joshajohnson/Hub20/production/1.0/photo.JPG

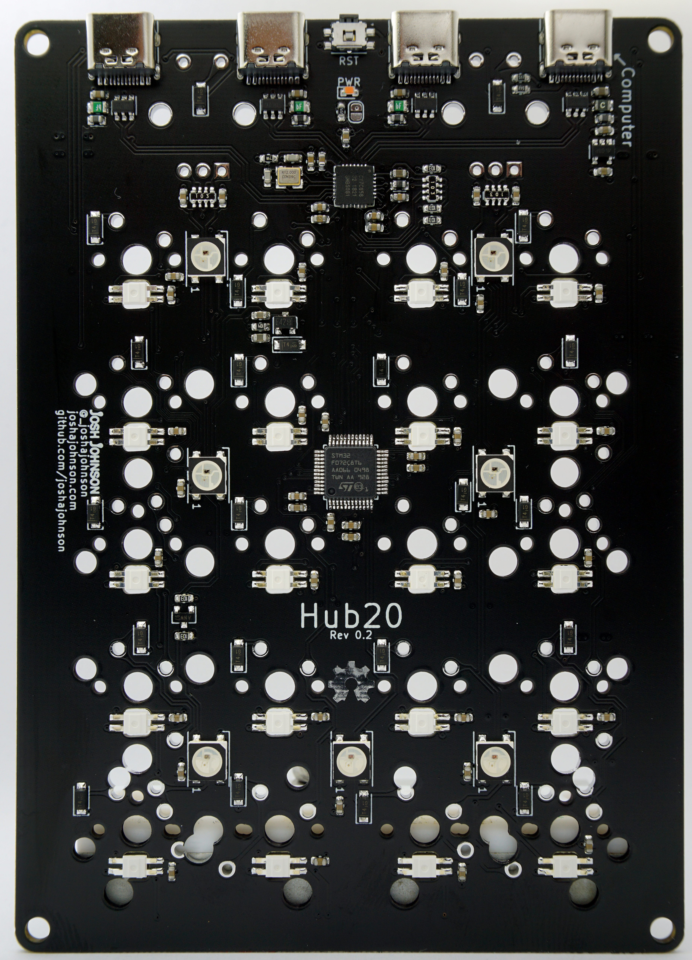
production/1.0/photo.JPG
