joshajohnson/Hub20/production/1.0/render.jpg

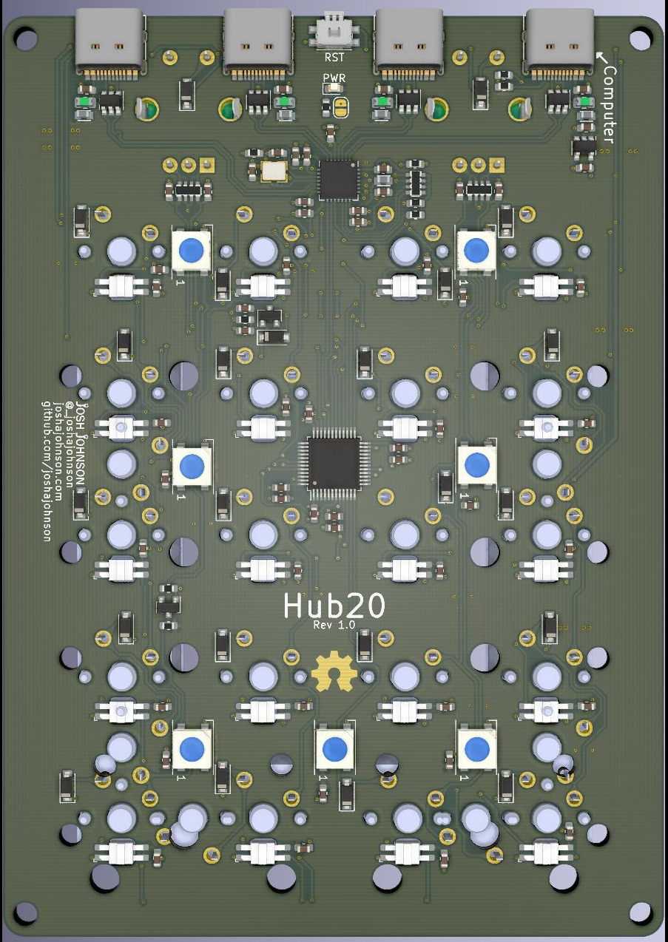
production/1.0/render.jpg
